NickLekas/Nixie-Clock/Hardware/Clock/Nixie Clock.sch

## EAGLE design Hardware/Clock/Nixie Clock.sch (2021-05-26)


Parts:
C1, C2, C3, C4: 0.1uF; C0603
R1: 10K; R0603
R2: 1M; R0603
U1: ATMEGA2560AU; TQFP100; MPN ATMEGA2560-16AU
X1: CSTCR6M00G53Z; CSTCR6M; MPN CSTCE16M0V13C99-R0

Connections:
+5V: C2.1, C3.1, C4.1, R1.2, U1.10 (VCC), U1.31 (VCC1), U1.61 (VCC2), U1.80 (VCC3)
DIM: U1.1 ((OC0B)PG5)
DST: U1.71 ((AD7)PA7)
DTR: C1.1
EIGHT: U1.74 ((AD4)PA4)
EXTRA1: U1.78 ((AD0)PA0)
FOUR: U1.75 ((AD3)PA3)
GND: C2.2, C3.2, C4.2, U1.11 (GND), U1.32 (GND1), U1.62 (GND2), U1.81 (GND3), U1.99 (AGND), X1.2
GPS_CTRL: U1.70 ((ALE)PG2)
GPS_RX: U1.64 (PJ1(TXD3/PCINT10))
GPS_TX: U1.63 (PJ0(RXD3/PCINT9))
HOA: U1.42 (PL7)
HOB: U1.40 (PL5(OC5C))
HOC: U1.39 (PL4(OC5B))
HOD: U1.41 (PL6)
HTA: U1.38 (PL3(OC5A))
HTB: U1.36 (PL1(ICP5))
HTC: U1.35 (PL0(ICP4))
HTD: U1.37 (PL2(T5))
LIGHT: U1.97 ((ADC0)PF0)
MISO: U1.22 ((MISO/PCINT3)PB3)
MOA: U1.60 ((A15)PC7)
MOB: U1.58 ((A13)PC5)
MOC: U1.57 ((A12)PC4)
MOD: U1.59 ((A14)PC6)
MOSI: U1.21 ((MOSI/PCINT2)PB2)
MTA: U1.56 ((A11)PC3)
MTB: U1.54 ((A9)PC1)
MTC: U1.53 ((A8)PC0)
MTD: U1.55 ((A10)PC2)
unnamed: R2.2, U1.34 (XTAL1), X1.3
unnamed: R2.1, U1.33 (XTAL2), X1.1
ONE: U1.77 ((AD1)PA1)
PLUS_MINUS: U1.73 ((AD5)PA5)
RST: C1.2, R1.1, U1.30 (RESET)
RTC_INT: U1.6 ((OC3B/INT4)PE4)
RXI: U1.3 ((TXD0)PE1)
SCK: U1.20 ((SCK/PCINT1)PB1)
SCL: U1.43 ((SCL/INT0)PD0)
SDA: U1.44 ((SDA/INT1)PD1)
TIME_MODE: U1.72 ((AD6)PA6)
TWO: U1.76 ((AD2)PA2)
TXO: U1.2 ((RXD0/PCIN8)PE0)
VCCA: U1.98 (AREF), U1.100 (AVCC)

Notes on the sheet:
Miccrocontroller
1.0

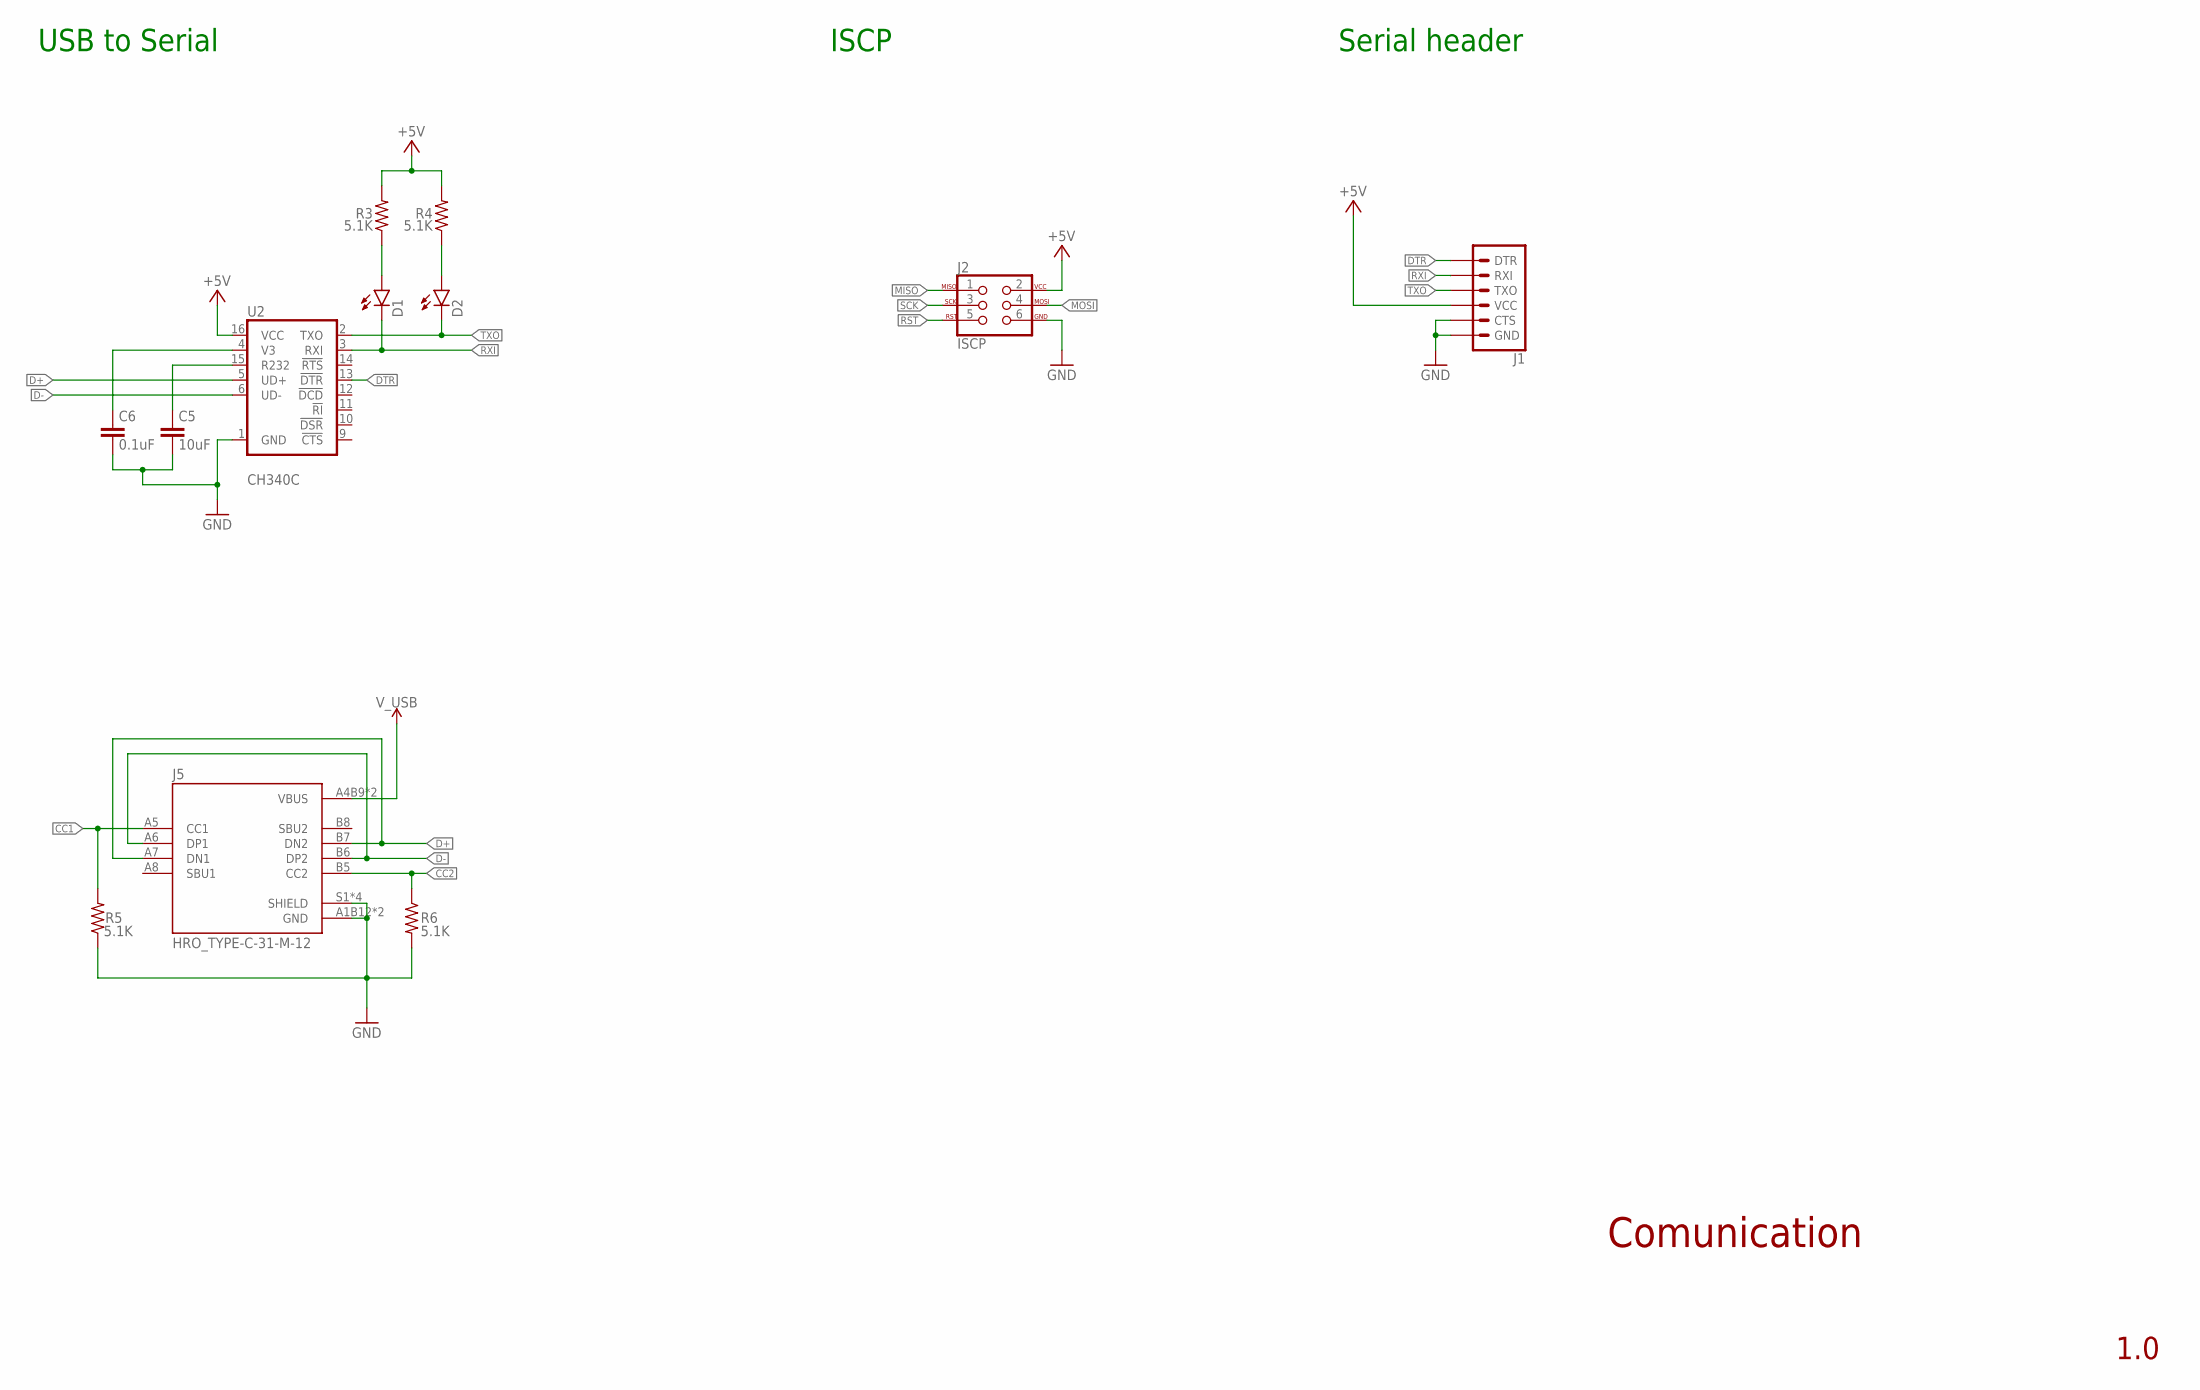
[picture p23: schematic Nixie Clock.sch, sheet 2]

Parts:
C5: 10uF; C0603
C6: 0.1uF; C0603
D1, D2: LEDCHIP-LED0603; CHIP-LED0603
J1: 6_PIN_SERIAL_TARGETSILK; 6_PIN_SERIAL_TARGET_SIDE_W_SILK
J2: ISCP; 2X3
J5: HRO_TYPE-C-31-M-12
R3, R4, R5, R6: 5.1K; R0603
U2: CH340C; SO016; MPN CH340C

Connections:
+5V: J1.P$4 (VCC), J2.2, R3.2, R4.2, U2.16 (VCC)
CC1: J5.A5 (CC1), R5.2
CC2: J5.B5 (CC2), R6.1
D+: J5.A7 (DN1), J5.B7 (DN2), U2.5 (UD+)
D-: J5.A6 (DP1), J5.B6 (DP2), U2.6 (UD-)
DTR: J1.P$1 (DTR), U2.13 (!DTR)
GND: C5.2, C6.2, J1.P$5 (CTS), J1.P$6 (GND), J2.6, J5.A1B12 (GND), J5.S1 (SHIELD), R5.1, R6.2, U2.1 (GND)
MISO: J2.1
MOSI: J2.4
unnamed: C5.1, U2.15 (R232)
unnamed: C6.1, U2.4 (V3)
unnamed: D1.A, R3.1
unnamed: D2.A, R4.1
RST: J2.5
RXI: D1.C, J1.P$3 (RXI), U2.3 (RXI)
SCK: J2.3
TXO: D2.C, J1.P$2 (TXO), U2.2 (TXO)
V_USB: J5.A4B9 (VBUS)

Notes on the sheet:
USB to Serial
Comunication
1.0
ISCP
Serial header


Parts:
3V3, 5V, 5V_ANALOG, 170V: TPPAD1-13; P1-13
C7, C8, C15: 1uF; C0603
C13: 100uF; C0603
C14: 4.7uF; E3,5-8
C16: 10uF; C0603
C17, C18: 0.22uF; C0603
DIM: TPPAD1-13; P1-13
R7, R8, R9: 100K; R0603
R10, R11: 10K; R0603
SJ1: SJ2W; SJ_2
T1: PZTA92; SOT223
T2: PZTA42; SOT223
T3: CSD18543Q3A; VSONP-8
U7: NCH8200HV
U9: MIC5504-3.3YM5TR; SOT95P280X130-5N; MPN MIC5504-3.3YM5-TR
U12: IP2721; TSSOP16EXP
U13: LM340MP-05; SOT223; MPN LM340MP-5.0/NOPB
U14: LM340MP-05; SOT223
VOUT: TPPAD1-13; P1-13
V_USB: TPPAD1-13; P1-13

Connections:
+3V3: 3V3.TP, C7.1, U9.5 (OUT)
+5V: 5V.TP, C8.1, U9.1 (IN), U9.3 (EN), U13.3 (VO)
ANODE: T1.2 (C)
CC1: U12.13 (CC1)
CC2: U12.12 (CC2)
DIM: DIM.TP, R10.2, R11.1
GND: C7.2, C8.2, C13.2, C14.-, C15.2, C16.2, C17.2, C18.2, R11.2, SJ1.3, T2.3 (E), U7.3 (GND), U9.2 (GND), U12.5 (GND), U13.4 (GND), U14.4 (GND)
unnamed: T3.4 (G), U12.1 (VBUSG)
unnamed: SJ1.2, U12.11 (SEL)
unnamed: R10.1, T2.1 (B)
unnamed: 170V.TP, C14.+, R7.2, T1.3 (E), U7.2 (VOUT)
unnamed: R7.1, R8.1, T1.1 (B)
unnamed: R9.2, T2.2 (C)
unnamed: R8.2, R9.1
VCCA: 5V_ANALOG.TP, U14.3 (VO)
VOUT: C13.1, C16.1, C17.1, C18.1, T3.5 (D), U7.1 (VCC), U12.16 (VBUS), U13.1 (VI), U14.1 (VI), VOUT.TP
V_USB: C15.1, SJ1.1, T3.1 (S), U12.2 (VIN), V_USB.TP

Notes on the sheet:
Nixie Power
3.3V
Power
1.0
USB PD
5V Analog

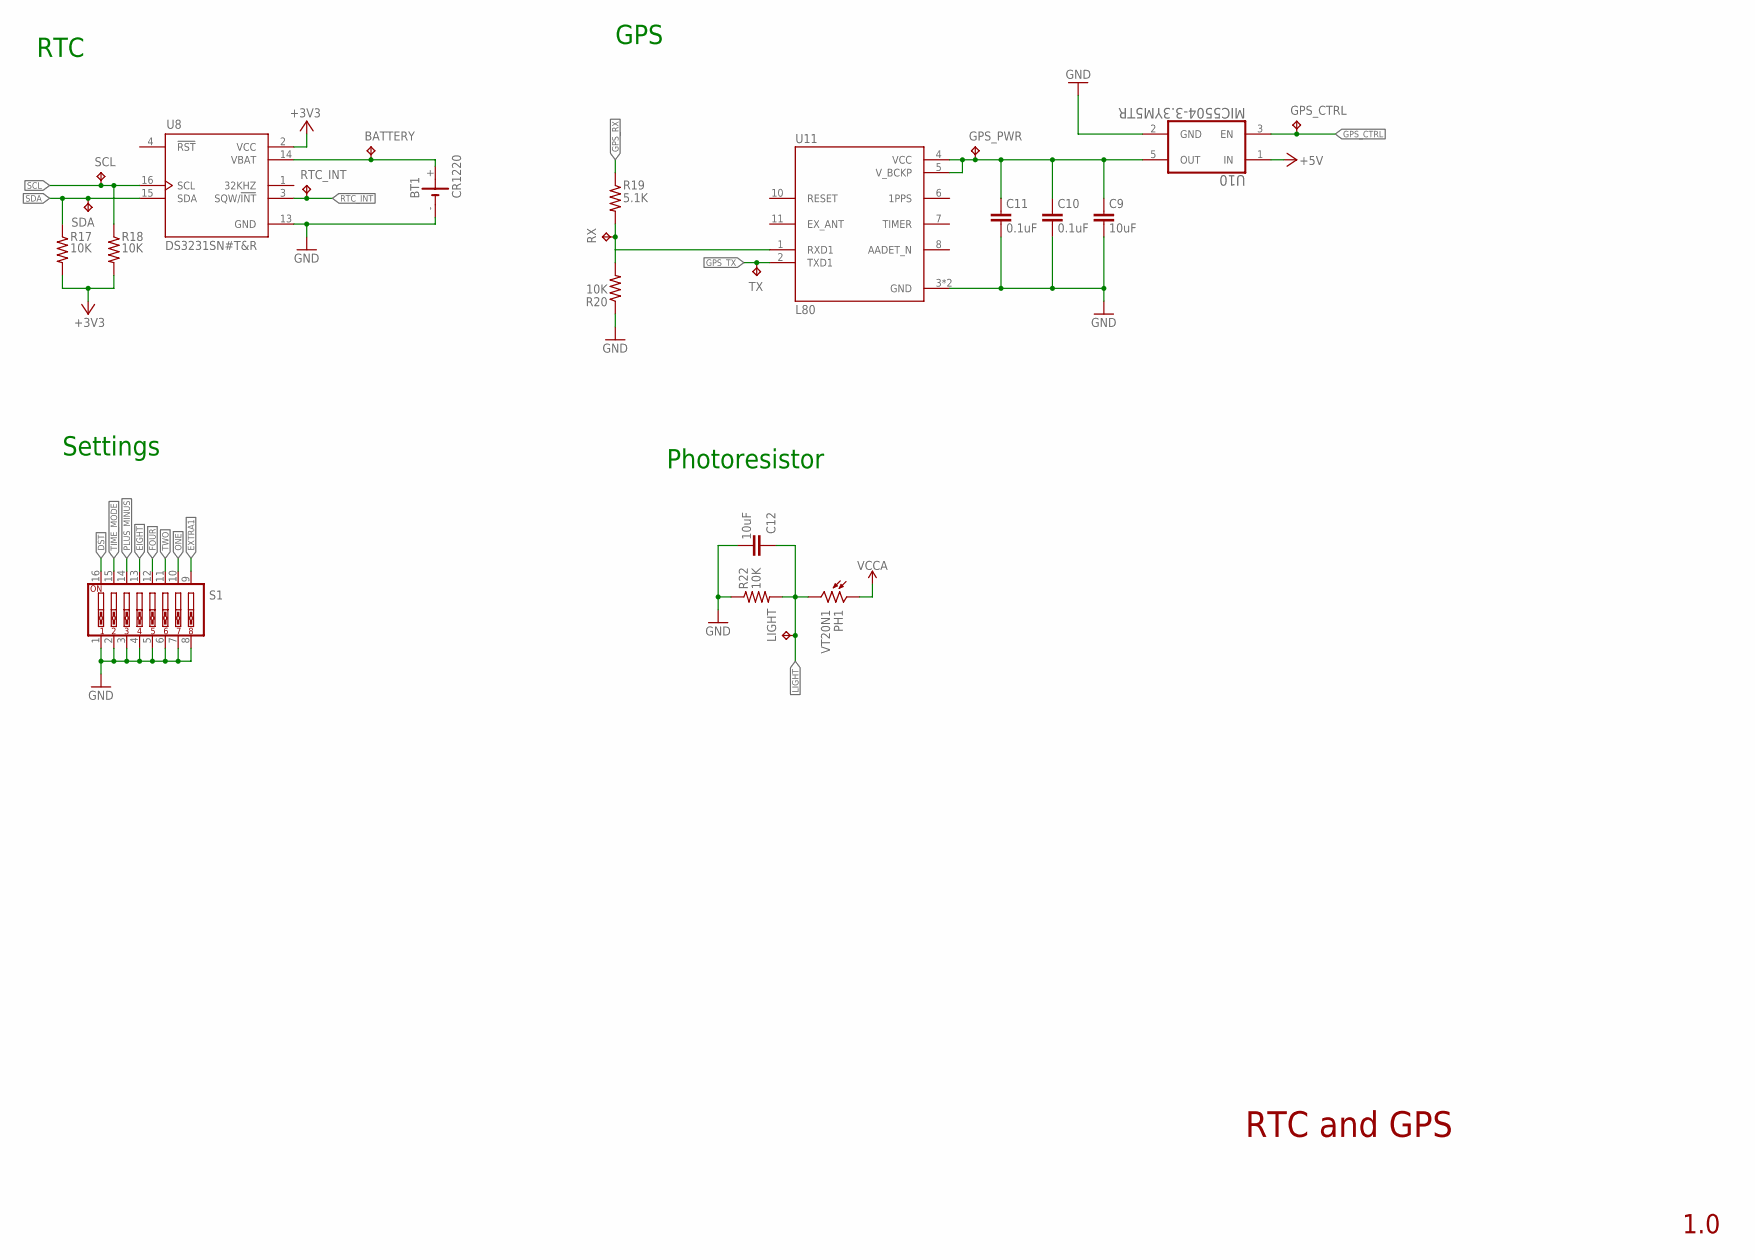
[picture p24: schematic Nixie Clock.sch, sheet 4]

Parts:
BATTERY: TPPAD1-13; P1-13
BT1: CR1220; CH291-1220LF
C9, C12: 10uF; C0603
C10, C11: 0.1uF; C0603
GPS_CTRL: TPPAD1-13; P1-13
GPS_PWR: TPPAD1-13; P1-13
LIGHT: TPPAD1-13; P1-13
PH1: VT20N1; TO46-VT200
R17, R18, R20, R22: 10K; R0603
R19: 5.1K; R0603
RTC_INT: TPPAD1-13; P1-13
RX: TPPAD1-13; P1-13
S1: SW_DIP-8; EDG-08
SCL: TPPAD1-13; P1-13
SDA: TPPAD1-13; P1-13
TX: TPPAD1-13; P1-13
U8: DS3231SN#T&R; SOIC127P1032X265-16N
U10: MIC5504-3.3YM5TR; SOT95P280X130-5N; MPN MIC5504-3.3YM5-TR
U11: L80; XCVR_L80

Connections:
+3V3: R17.2, R18.2, U8.2 (VCC)
+5V: U10.1 (IN)
DST: S1.16
EIGHT: S1.13
EXTRA1: S1.9
FOUR: S1.12
GND: BT1.-, C9.2, C10.2, C11.2, C12.2, R20.1, R22.1, S1.1, S1.2, S1.3, S1.4, S1.5, S1.6, S1.7, S1.8, U8.13 (GND), U10.2 (GND), U11.3 (GND)
GPS_CTRL: GPS_CTRL.TP, U10.3 (EN)
GPS_RX: R19.1
GPS_TX: TX.TP, U11.2 (TXD1)
LIGHT: C12.1, LIGHT.TP, PH1.2, R22.2
unnamed: BATTERY.TP, BT1.+, U8.14 (VBAT)
unnamed: C9.1, C10.1, C11.1, GPS_PWR.TP, U10.5 (OUT), U11.4 (VCC), U11.5 (V_BCKP)
unnamed: R19.2, R20.2, RX.TP, U11.1 (RXD1)
ONE: S1.10
PLUS_MINUS: S1.14
RTC_INT: RTC_INT.TP, U8.3 (SQW/!INT)
SCL: R18.1, SCL.TP, U8.16 (SCL)
SDA: R17.1, SDA.TP, U8.15 (SDA)
TIME_MODE: S1.15
TWO: S1.11
VCCA: PH1.1

Notes on the sheet:
RTC
GPS
RTC and GPS
1.0
Settings
Photoresistor


Parts:
ANODE: TPPAD1-13; P1-13
J3, J4: CONN_02LOCK_LONGPADS; 1X02_LOCK_LONGPADS
N1, N2, N3, N4: ИН-8; IN-8_SOCKET
R12, R13, R14, R15: 10k; M0805
R16: 100k; R0603
U3, U4, U5, U6: K155ID1; DIL16-KIT

Connections:
+5V: U3.5 (VCC), U4.5 (VCC), U5.5 (VCC), U6.5 (VCC)
ANODE: ANODE.TP, R12.1, R13.1, R14.1, R15.1, R16.1
GND: J4.1, U3.12 (GND), U4.12 (GND), U5.12 (GND), U6.12 (GND)
HOA: U4.3 (A)
HOB: U4.6 (B)
HOC: U4.7 (C)
HOD: U4.4 (D)
HTA: U3.3 (A)
HTB: U3.6 (B)
HTC: U3.7 (C)
HTD: U3.4 (D)
MOA: U6.3 (A)
MOB: U6.6 (B)
MOC: U6.7 (C)
MOD: U6.4 (D)
MTA: U5.3 (A)
MTB: U5.6 (B)
MTC: U5.7 (C)
MTD: U5.4 (D)
unnamed: J3.1, R16.2
unnamed: J3.2, J4.2
unnamed: N1.9, U3.2 (9)
unnamed: N1.8, U3.1 (8)
unnamed: N1.7, U3.10 (7)
unnamed: N1.6, U3.11 (6)
unnamed: N1.5, U3.14 (5)
unnamed: N1.4, U3.13 (4)
unnamed: N1.3, U3.9 (3)
unnamed: N1.2, U3.8 (2)
unnamed: N1.1, U3.15 (1)
unnamed: N1.0, U3.16 (0)
unnamed: N1.A, R12.2
unnamed: N2.9, U4.2 (9)
unnamed: N2.8, U4.1 (8)
unnamed: N2.7, U4.10 (7)
unnamed: N2.6, U4.11 (6)
unnamed: N2.5, U4.14 (5)
unnamed: N2.4, U4.13 (4)
unnamed: N2.3, U4.9 (3)
unnamed: N2.2, U4.8 (2)
unnamed: N2.1, U4.15 (1)
unnamed: N2.0, U4.16 (0)
unnamed: N2.A, R13.2
unnamed: N3.9, U5.2 (9)
unnamed: N3.8, U5.1 (8)
unnamed: N3.7, U5.10 (7)
unnamed: N3.6, U5.11 (6)
unnamed: N3.5, U5.14 (5)
unnamed: N3.4, U5.13 (4)
unnamed: N3.3, U5.9 (3)
unnamed: N3.2, U5.8 (2)
unnamed: N3.1, U5.15 (1)
unnamed: N3.0, U5.16 (0)
unnamed: N3.A, R14.2
unnamed: N4.9, U6.2 (9)
unnamed: N4.8, U6.1 (8)
unnamed: N4.7, U6.10 (7)
unnamed: N4.6, U6.11 (6)
unnamed: N4.5, U6.14 (5)
unnamed: N4.4, U6.13 (4)
unnamed: N4.3, U6.9 (3)
unnamed: N4.2, U6.8 (2)
unnamed: N4.1, U6.15 (1)
unnamed: N4.0, U6.16 (0)
unnamed: N4.A, R15.2

Notes on the sheet:
Nixie and Drivers
Nixie Tubes and Drivers
1.0
colon
