NickLekas/Nixie-Clock/Software/v1 - MEGA2560/Nixie-clock/include/debug.h

#ifndef DEBUG_H
#define DEBUG_H
#define DEBUG               // Enables the serial monitor

//debug options, setting to true prints debug data to the console
#define FIX_DEBUG           // Prints the GPS fix status
//#define TIME_DEBUG          // Prints the most recent time update
//#define GENERAL_DEBUG       // Prints general debug messages
//#define POWER_DEBUG         // Prints the debug messages for the power control
//#define SET_RTC             // Sets the RTC using the uploading computers time

//#define PCB                 //enables the pinout for the PCB clock instead of the MEGA

#endif
