NickLekas/Nixie-Clock/Software/src/power.cpp

#include "power.h"

STUSB4500 usbPD;

// Sets the 2 PDO voltages and calculates the currents for a given power limit
// PDO3 has top priority, PDO1 is fixed at 5V
void programPD() {
    int pdo2V = 9;                                          //9 volts
    int pdo2I = 2;                                          //2 amps

    Wire.begin();                                          // Initilaizes the STUB4500
    delay(100);                                             // Waits 0.1 seconds for the STUSB to startup

    if(!usbPD.begin()) {                                    // Checks if the STUSB connection was successful
        #ifdef POWER_DEBUG
            Serial.println("Cannot connect to STUSB4500");  // Prints that there was a connection error
        #endif
        while(1);                                           // Loops until the STUSB connetion is established
    }

    #ifdef POWER_DEBUG
        Serial.println("Connected to STUSB4500");           // Prints that the connection was made successfuly
    #endif

    delay(100);                                             // Waits 0.1 seconds for the STUSB to startup

    usbPD.write(DEFAULT);

    usbPD.setPdoNumber(2);                                  // Sets the STUSB to use 2 PDOs 

    //PDO1
    usbPD.setCurrent(1,0.75);                               // Sets the required current for PDO1
    usbPD.setUpperVoltageLimit(1,20);                       // Sets PDO1 voltage upper tolerance to 20%
    usbPD.setLowerVoltageLimit(1,20);                       // Sets PDO1 voltage lower tolerance to 20%

    //PDO2
    usbPD.setVoltage(2,pdo2V);                              // Sets the required voltage for PDO2
    usbPD.setCurrent(2,pdo2I);                              // Sets the required current for PDO2
    usbPD.setLowerVoltageLimit(2,20);                       // Sets PDO2 voltage upper tolerance to 20%
    usbPD.setUpperVoltageLimit(2,20);                       // Sets PDO2 voltage lower tolerance to 20%

    usbPD.write();

    #ifdef POWER_DEBUG
        Serial.println("Programmed");                       // Prints that the STUSB was programmed
    #endif

    return;
}
